sashankthapa/fingertip-fusion-hw/exports/images/USB-C.png

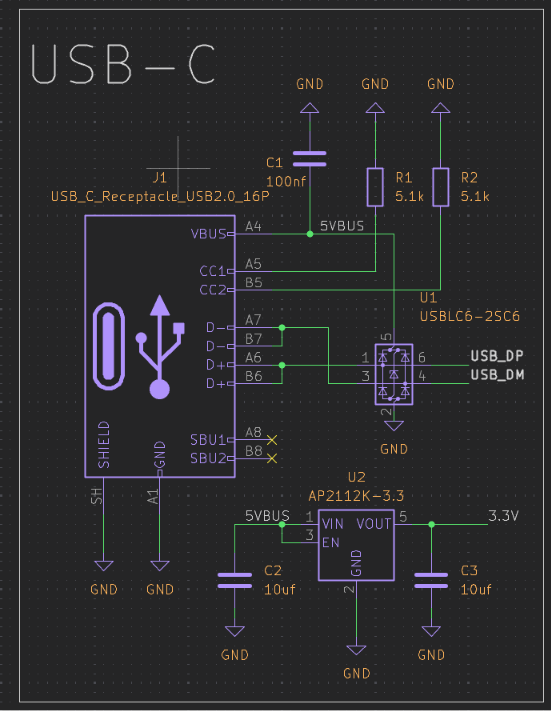
exports/images/USB-C.png
